lennon101/CC3501-Security-System-Assignment/SecuritySystem/src/c.jpg

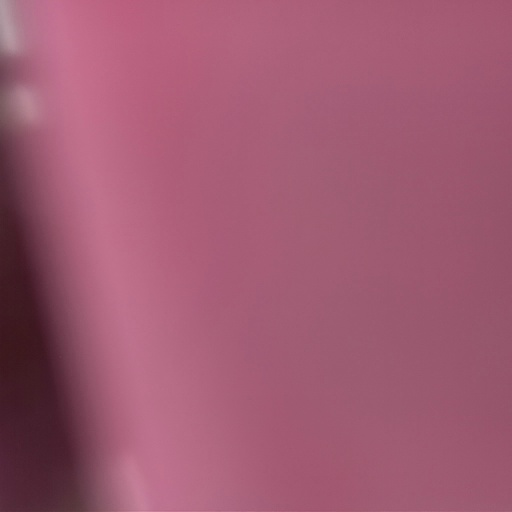
SecuritySystem/src/c.jpg
