lennon101/CC3501-Security-System-Assignment/SecuritySystem/src/frame1.jpg

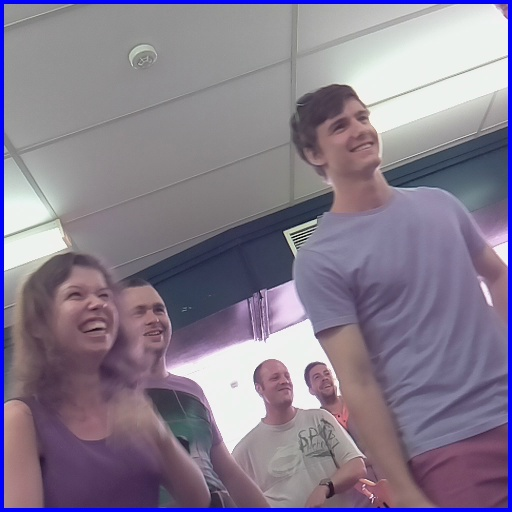
SecuritySystem/src/frame1.jpg
