lennon101/CC3501-Security-System-Assignment/SecuritySystem/src/images/1.png

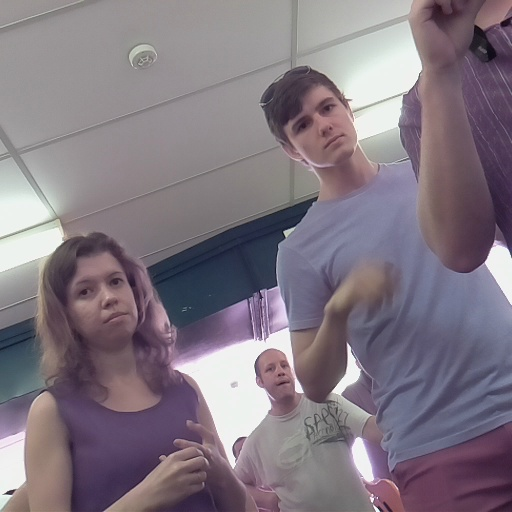
SecuritySystem/src/images/1.png
