lennon101/CC3501-Security-System-Assignment/SecuritySystem/src/images/7.png

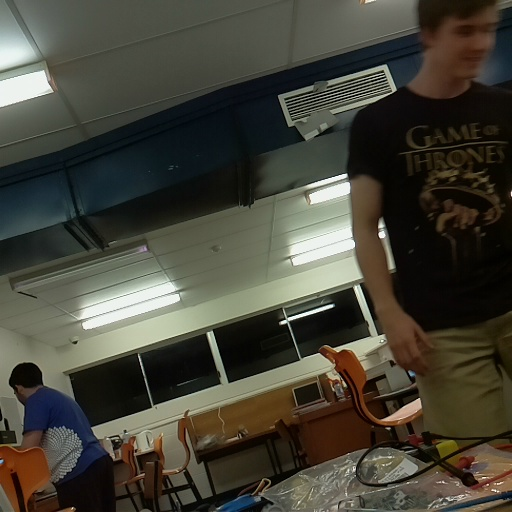
SecuritySystem/src/images/7.png
