lennon101/CC3501-Security-System-Assignment/SecuritySystem/src/images/9.png

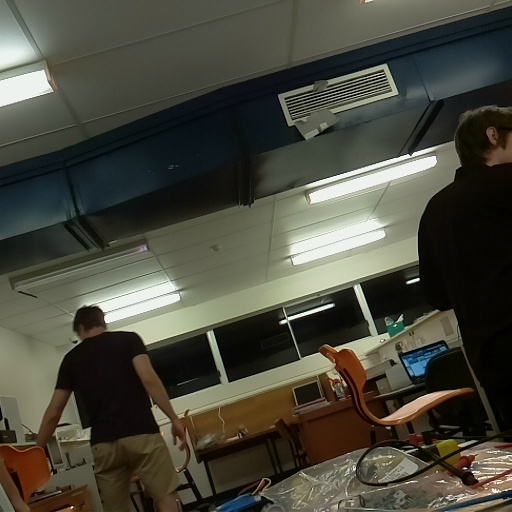
SecuritySystem/src/images/9.png
