lennon101/CC3501-Security-System-Assignment/SecuritySystem/src/images/10.png

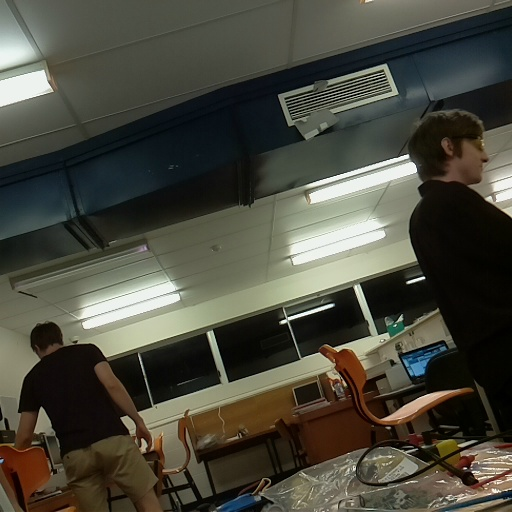
SecuritySystem/src/images/10.png
